fusuian/PP2PS2/sw_data_t.h

// The structure sw_data_t is :
//
// Copyright (c) 2013, Peter
// All rights reserved.
// see "Simplified BSD License" or "FreeBSD License"
// from SidewinderInterface https://github.com/MaZderMind/SidewinderInterface


#ifndef _SW_DATA_T_
#define _SW_DATA_T_

// data structure as sent from my sidewinder device, 48 bits total
// this datatype is accessable via two ways: an integer-array and a struct
// the former is used to used to manipulate the data at a bit-level
// while the latter is used to access individual pieces of data
typedef union
{
  // the struct consisting of the various data-fields sent by the sidewinder device
  struct
  {
    unsigned int btn_fire:1;      // bit  1

    unsigned int btn_top:1;       // bit  2
    unsigned int btn_top_up:1;    // bit  3
    unsigned int btn_top_down:1;  // bit  4

    unsigned int btn_a:1;         // bit  5
    unsigned int btn_b:1;         // bit  6
    unsigned int btn_c:1;         // bit  7
    unsigned int btn_d:1;         // bit  8

    unsigned int btn_shift:1;     // bit  9

    unsigned int x:10;            // bits 10-19
    unsigned int y:10;            // bits 20-29
    unsigned int m:7;             // bits 30-36
    unsigned int r:6;             // bits 37-42

    unsigned int head:4;          // bits 43-46

    unsigned int reserved:1;      // bit 47
    unsigned int parity:1;        // bit 48

    unsigned short blank;
  };

  // the ints are used to access the struct-data at bit-level
  unsigned char buf[6];
} sw_data_t;

#endif
